sparkfun/SparkFun_u-blox_MAX-M10S/docs/assets/18037-SparkFun_GNSS_Receiver_Breakout_-_MAX-M10S__Qwiic_-01.jpg

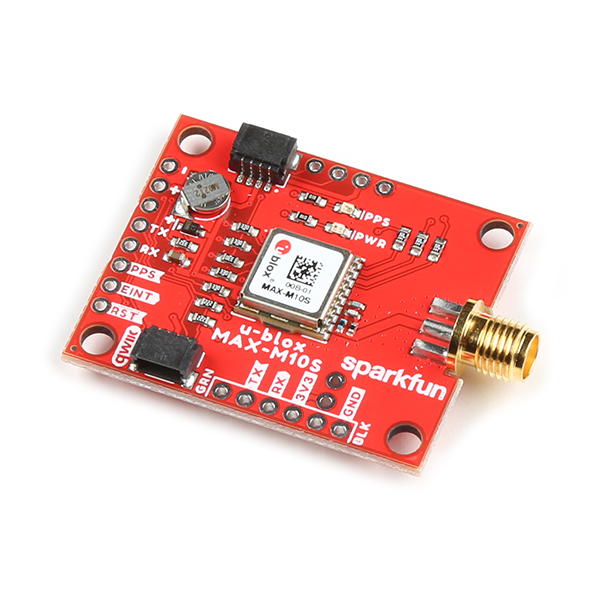
docs/assets/18037-SparkFun_GNSS_Receiver_Breakout_-_MAX-M10S__Qwiic_-01.jpg
